adrielluiz/platform_tactile_acquisition/3D_files/guia200_5mm.SLDPRT

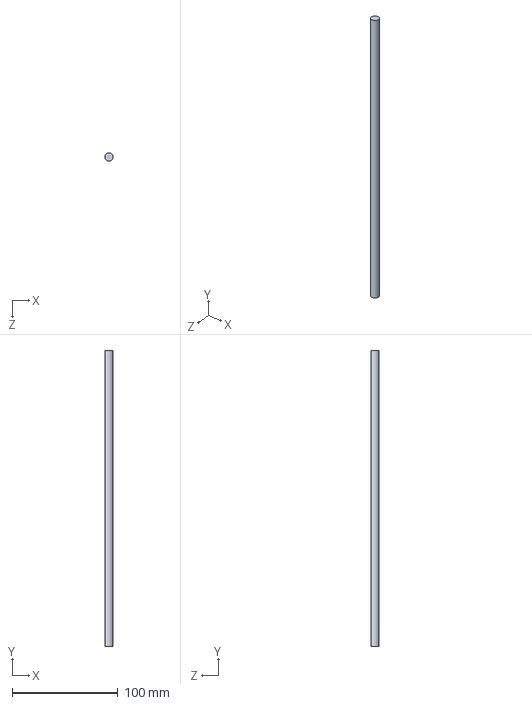
[picture p17: CAD file, 2023-06-17]
3D_files/guia200_5mm.SLDPRT
8.00 x 280.5 x 8.00 mm
