adrielluiz/platform_tactile_acquisition/3D_files/fusoTrapazoidal172_5mm.SLDPRT

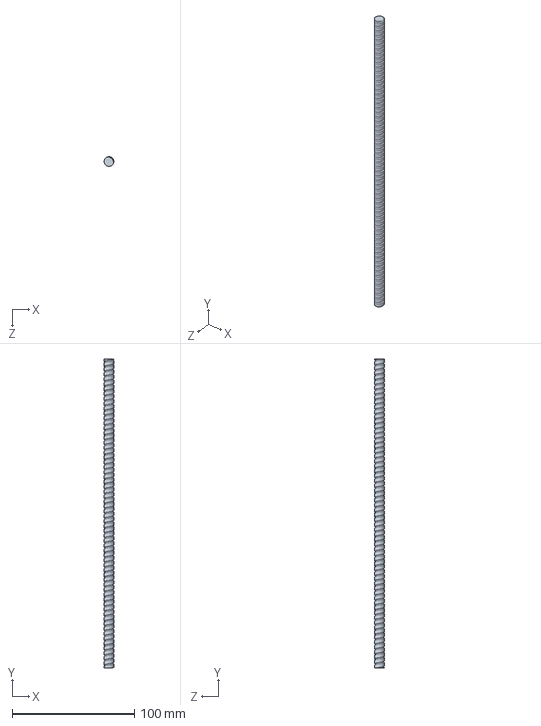
[picture p18: CAD file, 2023-06-17]
3D_files/fusoTrapazoidal172_5mm.SLDPRT
8.00 x 252.5 x 8.00 mm
