adrielluiz/platform_tactile_acquisition/3D_files/cantoneira.SLDPRT

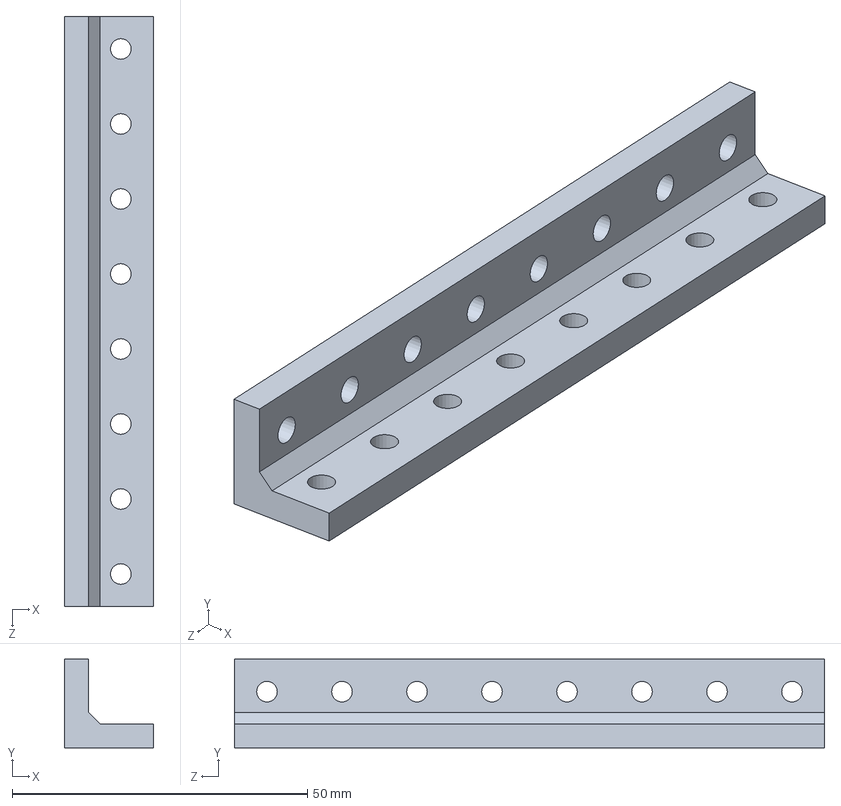
[picture p19: CAD file, 2023-06-17]
3D_files/cantoneira.SLDPRT
15.0 x 15.0 x 100.0 mm
