adrielluiz/platform_tactile_acquisition/3D_files/SuporteMotor.SLDPRT

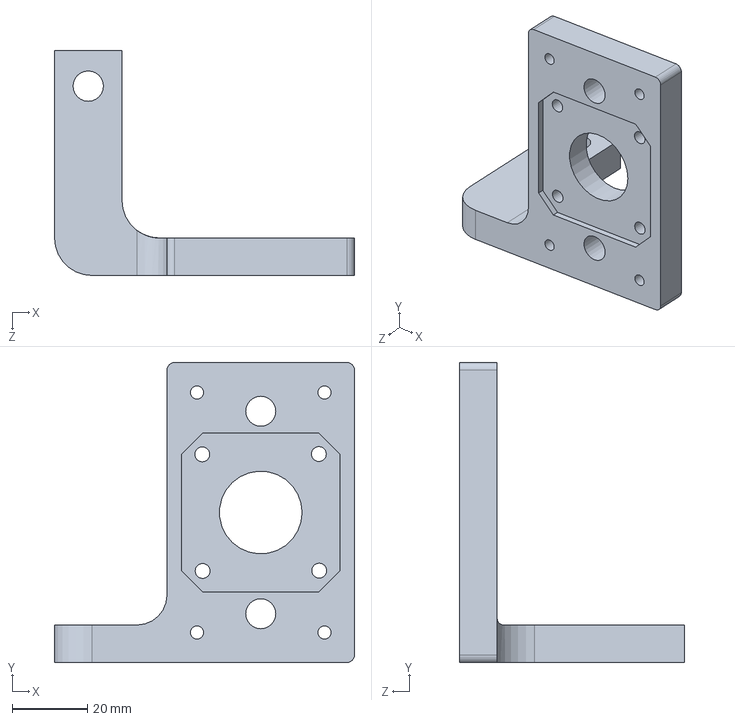
[picture p20: CAD file, 2023-06-17]
3D_files/SuporteMotor.SLDPRT
80.0 x 80.0 x 60.0 mm
