adrielluiz/platform_tactile_acquisition/3D_files/guia240mm.SLDPRT

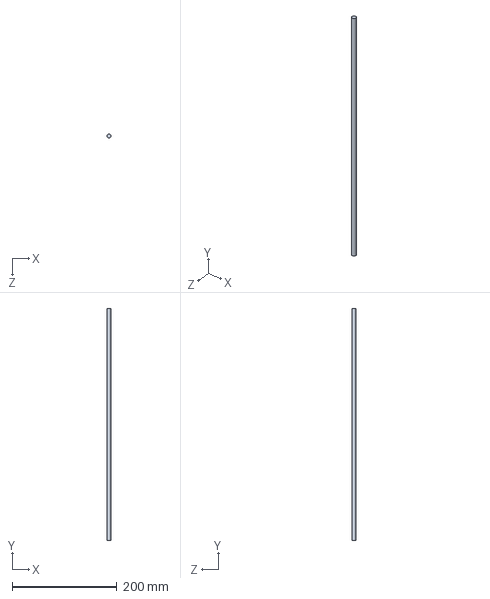
[picture p21: CAD file, 2023-06-17]
3D_files/guia240mm.SLDPRT
8.00 x 443.0 x 8.00 mm
