adrielluiz/platform_tactile_acquisition/3D_files/acoplador_guiamotor.SLDPRT

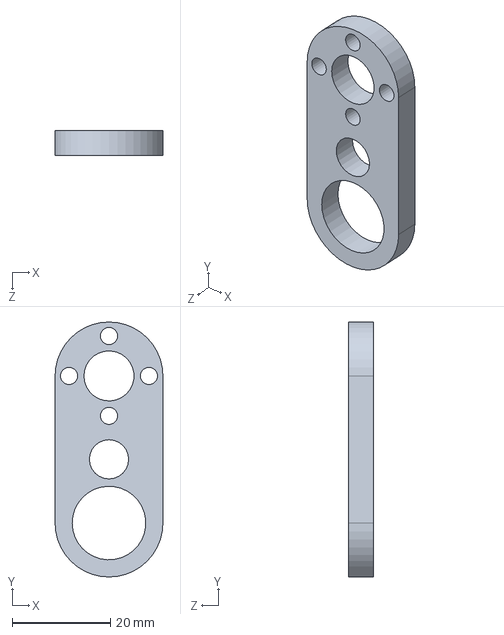
[picture p22: CAD file, 2023-06-17]
3D_files/acoplador_guiamotor.SLDPRT
22.0 x 52.0 x 5.00 mm
