adrielluiz/platform_tactile_acquisition/3D_files/plataforma.SLDPRT

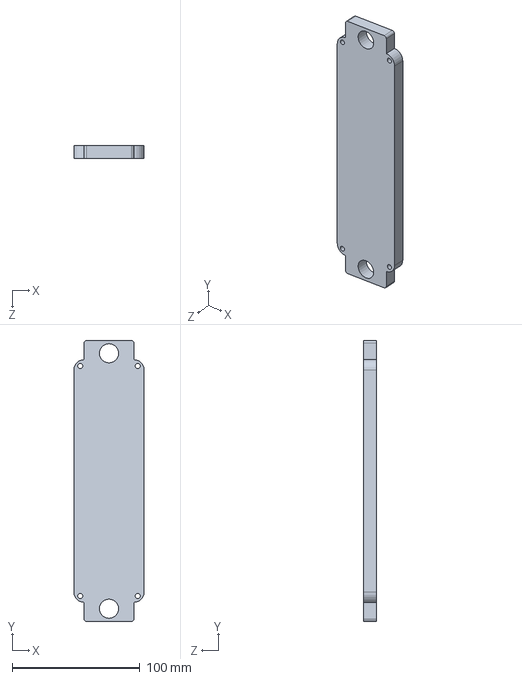
[picture p23: CAD file, 2023-06-17]
3D_files/plataforma.SLDPRT
55.0 x 220.0 x 10.0 mm
