adrielluiz/platform_tactile_acquisition/3D_files/RolamentoLinear.SLDPRT

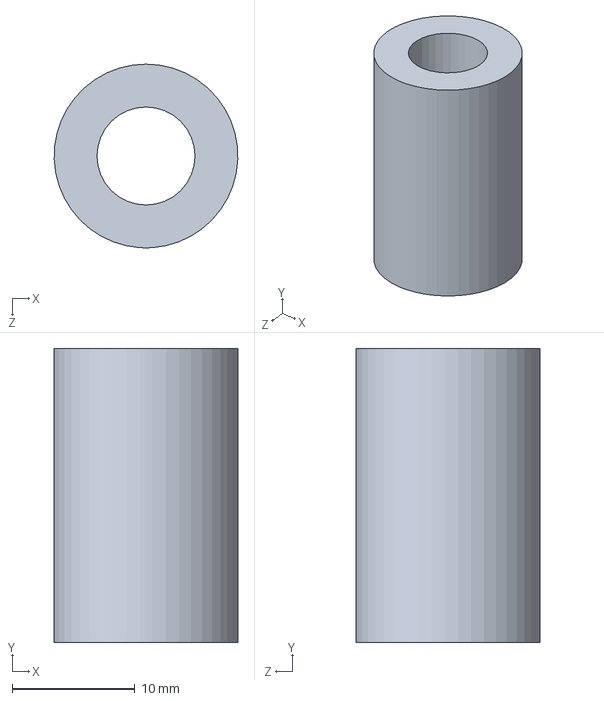
[picture p24: CAD file, 2023-06-17]
3D_files/RolamentoLinear.SLDPRT
15.0 x 24.0 x 15.0 mm
