adrielluiz/platform_tactile_acquisition/3D_files/suporteFusoGuiaMotor.SLDPRT

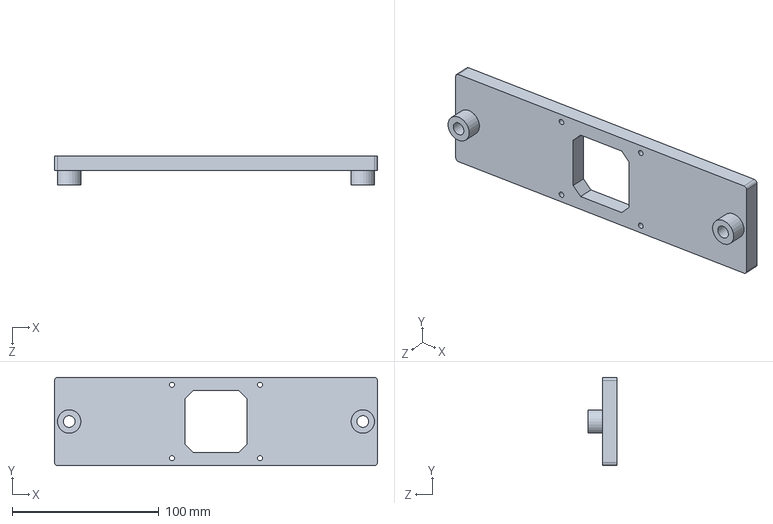
[picture p25: CAD file, 2023-06-17]
3D_files/suporteFusoGuiaMotor.SLDPRT
220.0 x 60.0 x 20.0 mm
