adrielluiz/platform_tactile_acquisition/3D_files/fusoTrapazoidal105_5mm.SLDPRT

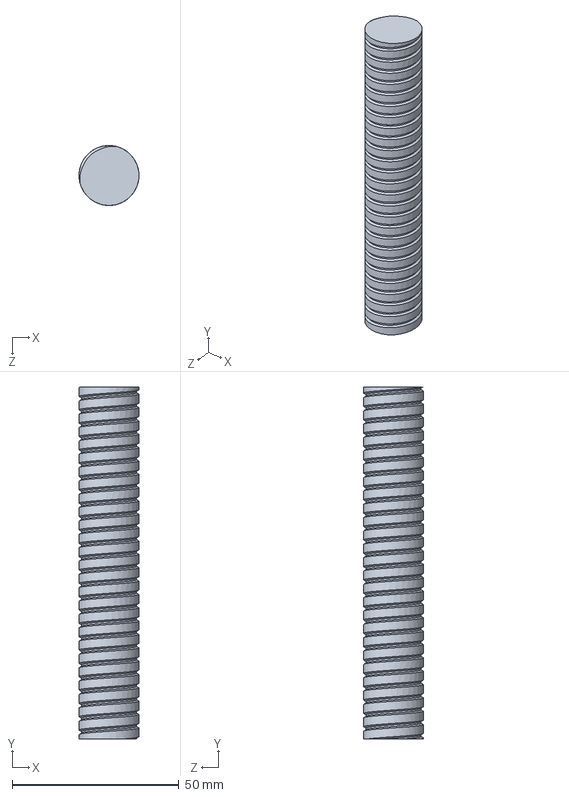
[picture p26: CAD file, 2023-06-17]
3D_files/fusoTrapazoidal105_5mm.SLDPRT
18.0 x 105.5 x 18.0 mm
