adrielluiz/platform_tactile_acquisition/3D_files/acoplador.SLDPRT

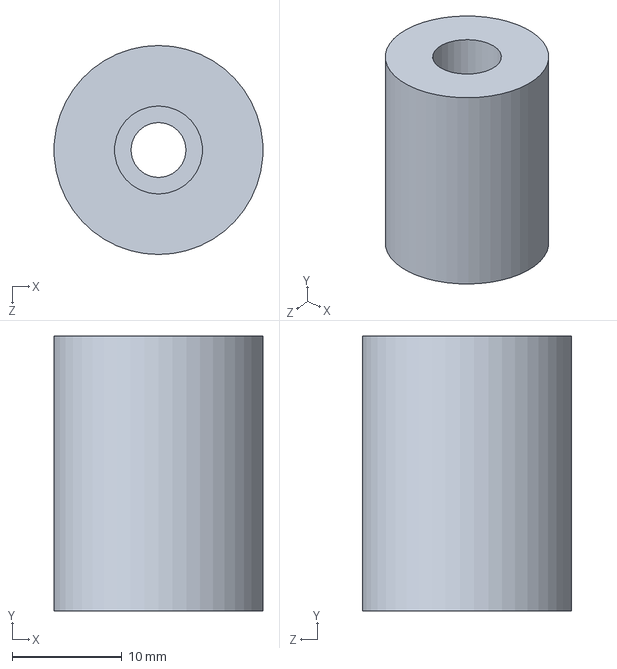
[picture p27: CAD file, 2023-06-17]
3D_files/acoplador.SLDPRT
19.0 x 25.0 x 19.0 mm
