adrielluiz/platform_tactile_acquisition/3D_files/fusoTrapazoidal240mm.SLDPRT

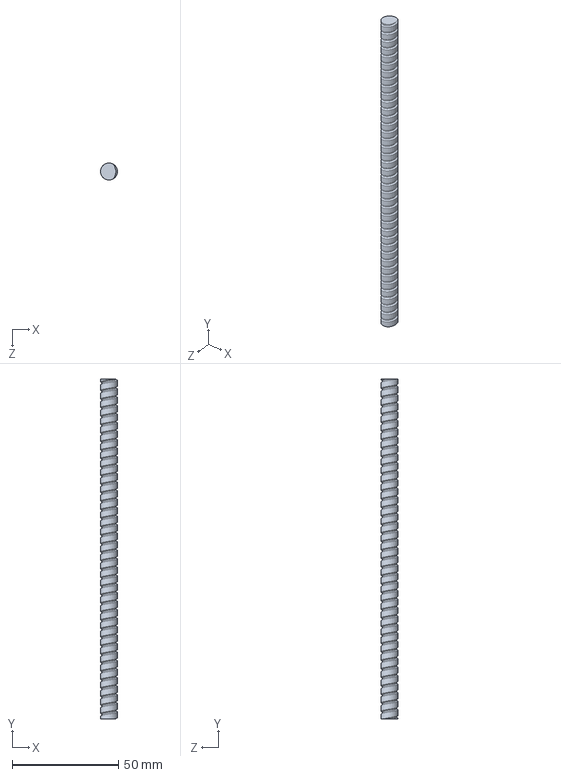
[picture p28: CAD file, 2023-06-17]
3D_files/fusoTrapazoidal240mm.SLDPRT
8.00 x 160.0 x 8.00 mm
