adrielluiz/platform_tactile_acquisition/3D_files/acrilico1.SLDPRT

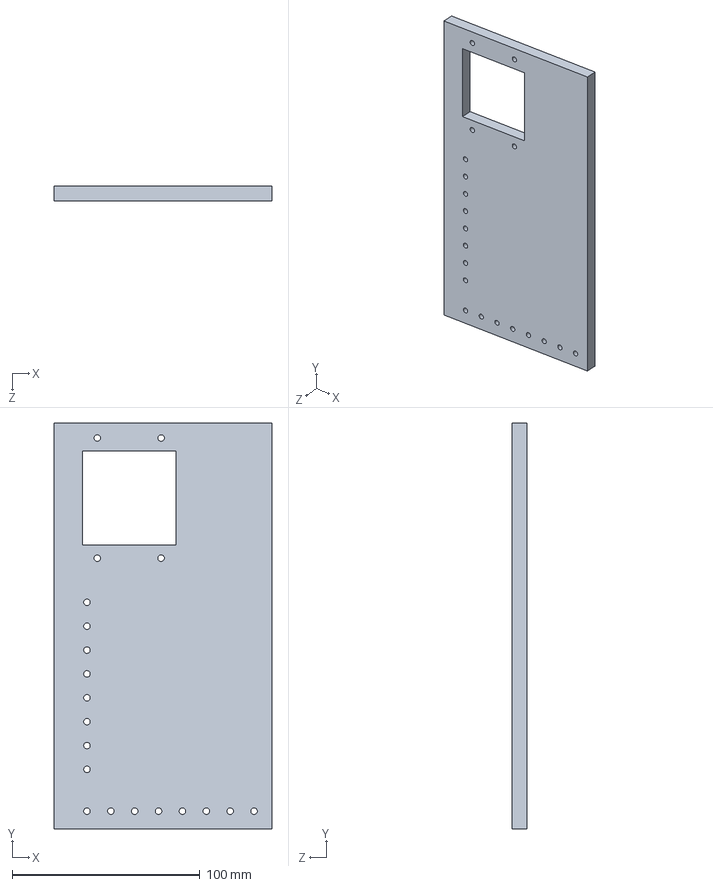
[picture p30: CAD file, 2023-06-17]
3D_files/acrilico1.SLDPRT
116.0 x 216.2 x 8.00 mm
