adrielluiz/platform_tactile_acquisition/3D_files/suportePlataforma.SLDPRT

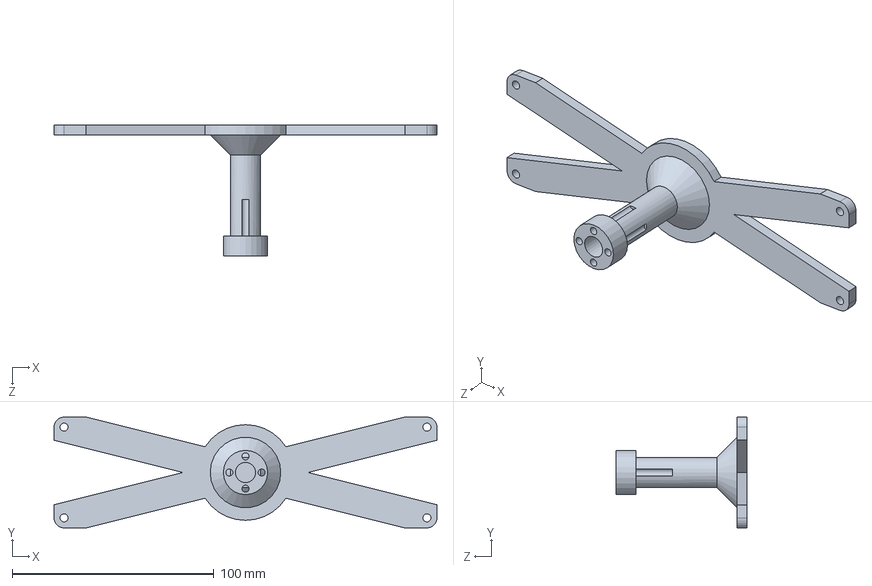
[picture p31: CAD file, 2023-06-17]
3D_files/suportePlataforma.SLDPRT
190.0 x 55.0 x 65.0 mm
