adrielluiz/platform_tactile_acquisition/3D_files/ContraApoioMotor.SLDPRT

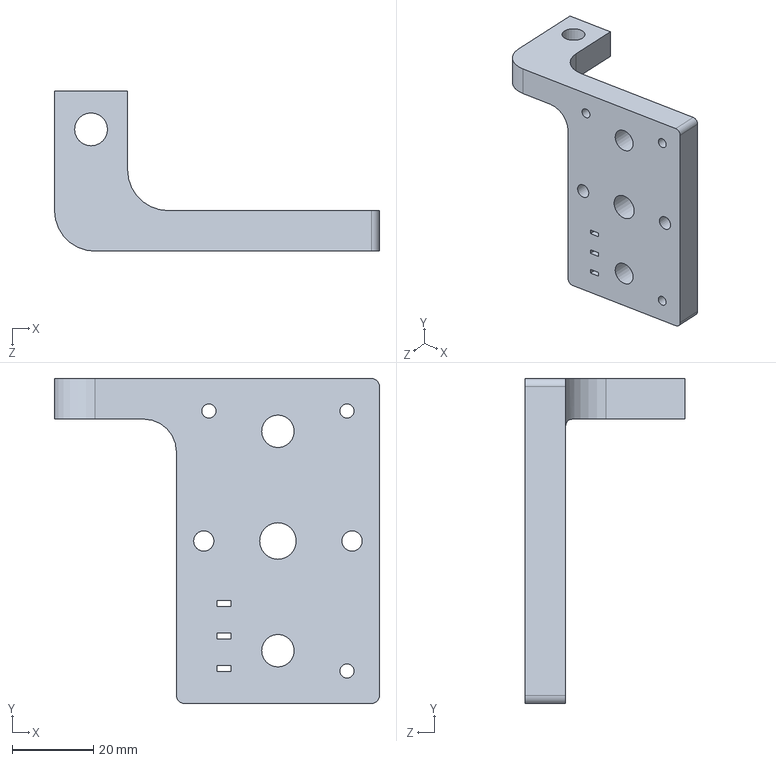
[picture p32: CAD file, 2023-06-17]
3D_files/ContraApoioMotor.SLDPRT
80.0 x 80.0 x 39.5 mm
