adrielluiz/platform_tactile_acquisition/3D_files/fusoTrapazoidal100_8mm.SLDPRT

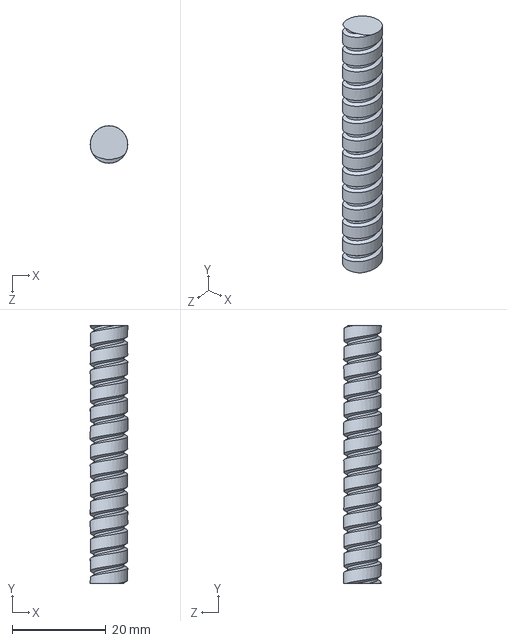
[picture p33: CAD file, 2023-06-17]
3D_files/fusoTrapazoidal100_8mm.SLDPRT
8.00 x 55.0 x 8.00 mm
