adrielluiz/platform_tactile_acquisition/3D_files/fuso240mm.SLDPRT

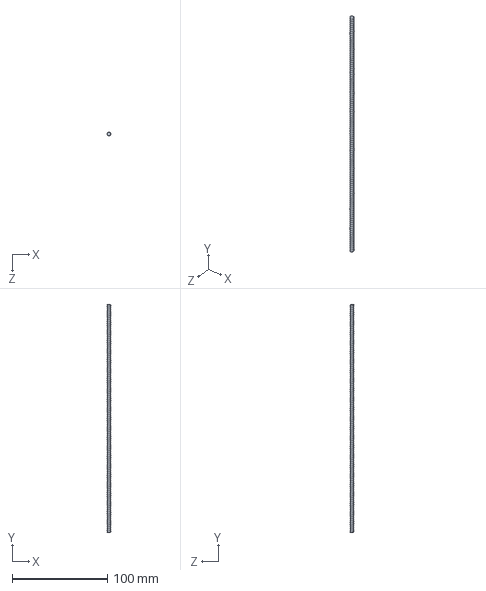
[picture p34: CAD file, 2023-06-17]
3D_files/fuso240mm.SLDPRT
4.00 x 240.0 x 4.00 mm
