adrielluiz/platform_tactile_acquisition/3D_files/box.SLDPRT

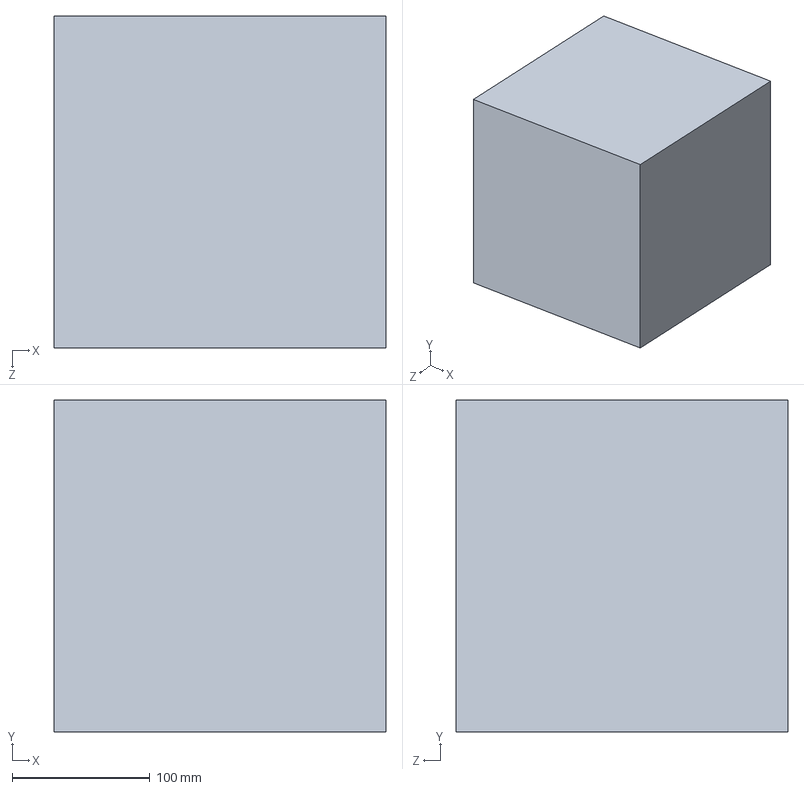
[picture p35: CAD file, 2023-06-17]
3D_files/box.SLDPRT
240.8 x 240.8 x 240.8 mm
