adrielluiz/platform_tactile_acquisition/FIRMWARE/V2/plataform_tact/include/motor.h

#pragma once

#define MOTOR1_STEP_MM 12
#define MOTOR2_STEP_MM 8


void motor_init(void);
void motor_set_speed(int motor_id, int speed_ms);
uint16_t motor_get_speed(int motor_id);
void motor_set_pos(int motor_id, int pos_um);
int motor_get_pos(int motor_id);
void motor_set_pos_home(int motor_id);
int motor_convert_steps_to_um(int motor_id, int pos_steps);
void motor_test_loop(void);
