adrielluiz/platform_tactile_acquisition/SOFTWARE/excel.py

import pandas as pd
import os

class Excel():
    def __init__(self):
        self.colX = []
        self.colZ = []
        self.colPosTs = []
        self.colFSR = []
        self.colMeas = []
        self.colMeasTs = []
        self.filename = "./plataform_data.xlsx"
        self.col_ts = []
        self.col_meas_load_cell = []
        self.col_resistive_sensor = []

    def clean_data(self):    
        self.colX = []
        self.colZ = []
        self.colPosTs = []
        self.colFSR = []
        self.colMeas = []
        self.colMeasTs = []
        self.col_ts = []
        self.col_meas_load_cell = []
        self.col_resistive_sensor = []

    def set_file_name(self, new_name):
        self.filename = new_name    

    def file_exists(self):
        return os.path.isfile(self.filename)    

    def get_unique_filename(self, file_name):
        name, ext = os.path.splitext(file_name)
        i = 0
        while os.path.exists(file_name):
            i += 1
            file_name = f"{name}[{i}]{ext}"
        return file_name

    def find_minimum_length(self, array1, array2, array3):
        lengths = [len(array1), len(array2), len(array3)]
        minimum_length = min(lengths)
        return minimum_length 
    
    def resize_arrays(self, array1, array2, array3):
        min_length = min(len(array1), len(array2), len(array3))
        array1 = array1[:min_length]
        array2 = array2[:min_length]
        array3 = array3[:min_length]
        return array1, array2, array3

    def save_file(self):
        d = dict(Timestamp = self.col_ts, LoadCell = self.col_meas_load_cell, ResistiveSensor = self.col_resistive_sensor)
        df = pd.DataFrame(dict([ (k,pd.Series(v)) for k,v in d.items() ]))
        self.filename = self.get_unique_filename(self.filename)
        df.to_excel(self.filename, index=False) 
        self.clean_data()

    def append_pos_x(self, pos_x):
        self.colX.append(pos_x)

    def append_pos_z(self, pos_z):
        self.colZ.append(pos_z)

    def append_fsr(self, fsr):
        self.colFSR.append(fsr)   
    
    def append_pos(self, pos_x, pos_z, ts):
        self.colX.append(pos_x)
        self.colZ.append(pos_z)
        self.colPosTs.append(ts)
    
    def append_meas(self, ts, meas):
        self.colMeasTs.append(ts) 
        self.colMeas.append(meas)   

    def append_meas_board(self, ts, loadcell, resistive_sensor):
        self.col_ts.append(ts) 
        self.col_meas_load_cell.append(loadcell) 
        self.col_resistive_sensor.append(resistive_sensor)
        
